Juanvvc/handler-adapters/output/adapter_20mm_double.png

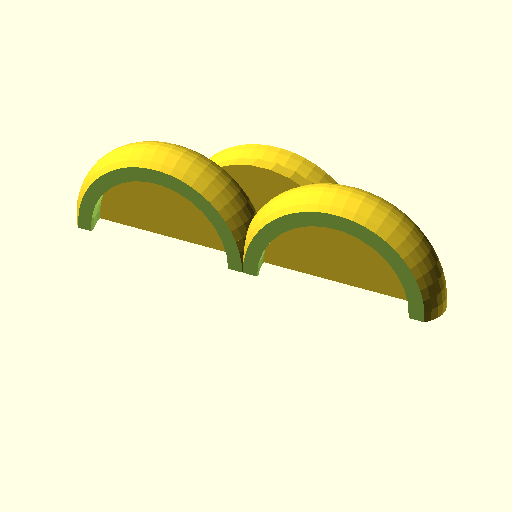
output/adapter_20mm_double.png
