Juanvvc/handler-adapters/output/adapter_20mm_double_3486254.png

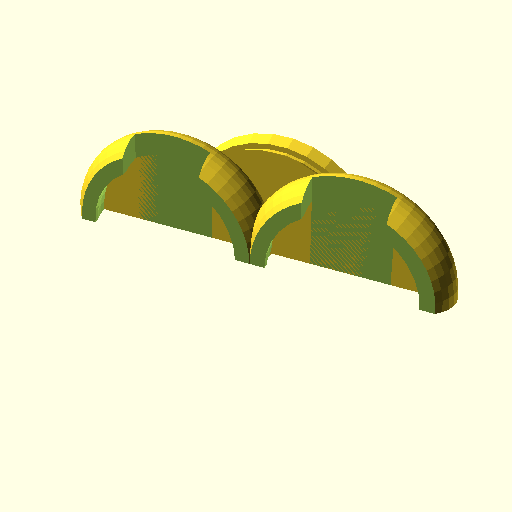
output/adapter_20mm_double_3486254.png
