Juanvvc/handler-adapters/output/adapter_25mm.png

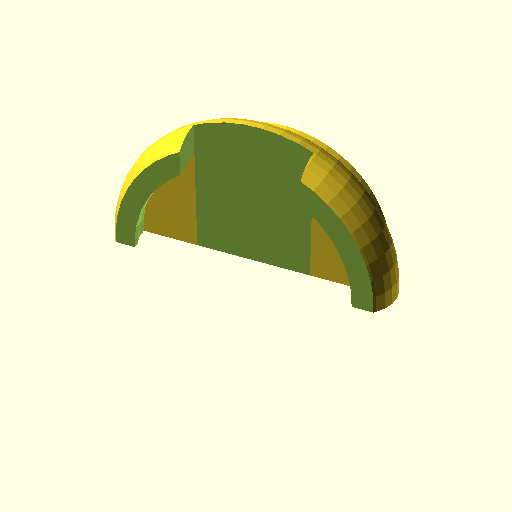
output/adapter_25mm.png
