Juanvvc/handler-adapters/output/adapter_30x50mm.png

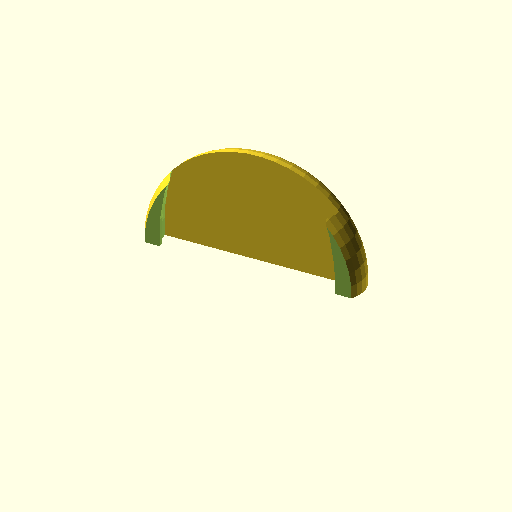
output/adapter_30x50mm.png
