Juanvvc/handler-adapters/handler_base.scad

include <handler_models.scad>

// similar to https://www.thingiverse.com/thing:3486254
//handler_base_detail=8; handler_base_h=17.5; handler_base_r=30; tolerance=1.01;

// tight base
//handler_base_detail=50; handler_base_h=17.5; handler_base_r=25; tolerance=1;

handler_base(handler_base_h, handler_base_r, handler_r, tolerance=tolerance, handler_base_detail=handler_base_detail);
